baranyazici/Omni-Wheel-Robot-Development-for-Industrial-Transportation/PCB/PCB_Photos/PCB_Photo_1.jpeg

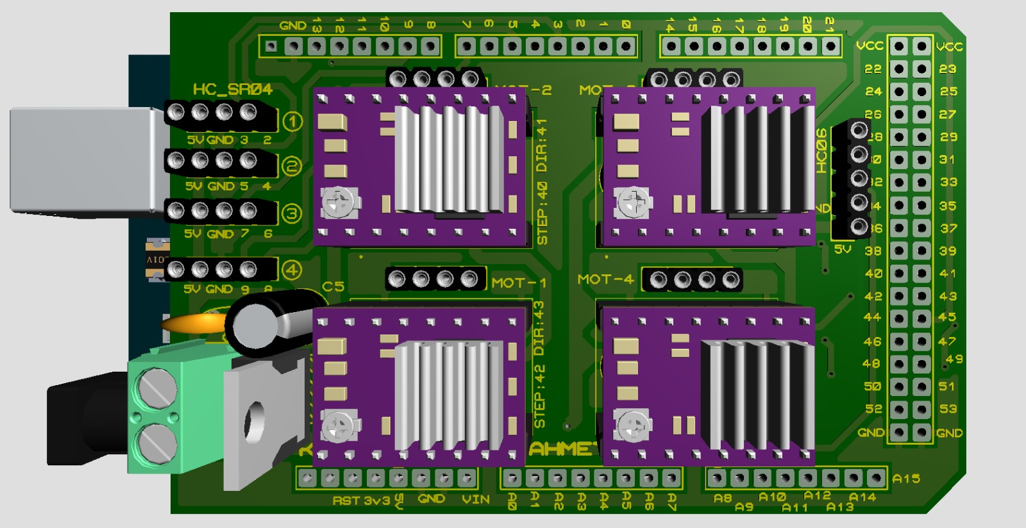
PCB/PCB_Photos/PCB_Photo_1.jpeg
