baranyazici/Omni-Wheel-Robot-Development-for-Industrial-Transportation/PCB/PCB_Photos/PCB_Photo_2.jpeg

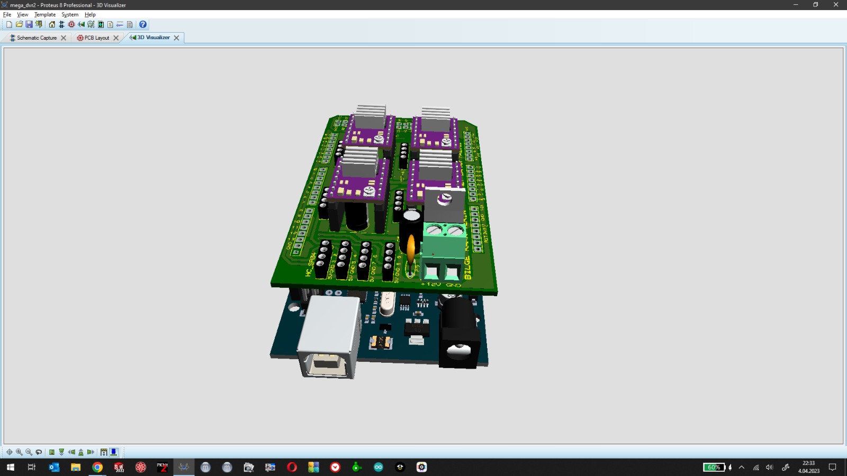
PCB/PCB_Photos/PCB_Photo_2.jpeg
