baranyazici/Omni-Wheel-Robot-Development-for-Industrial-Transportation/PCB/PCB_Photos/PCB_Photo_9.jpeg

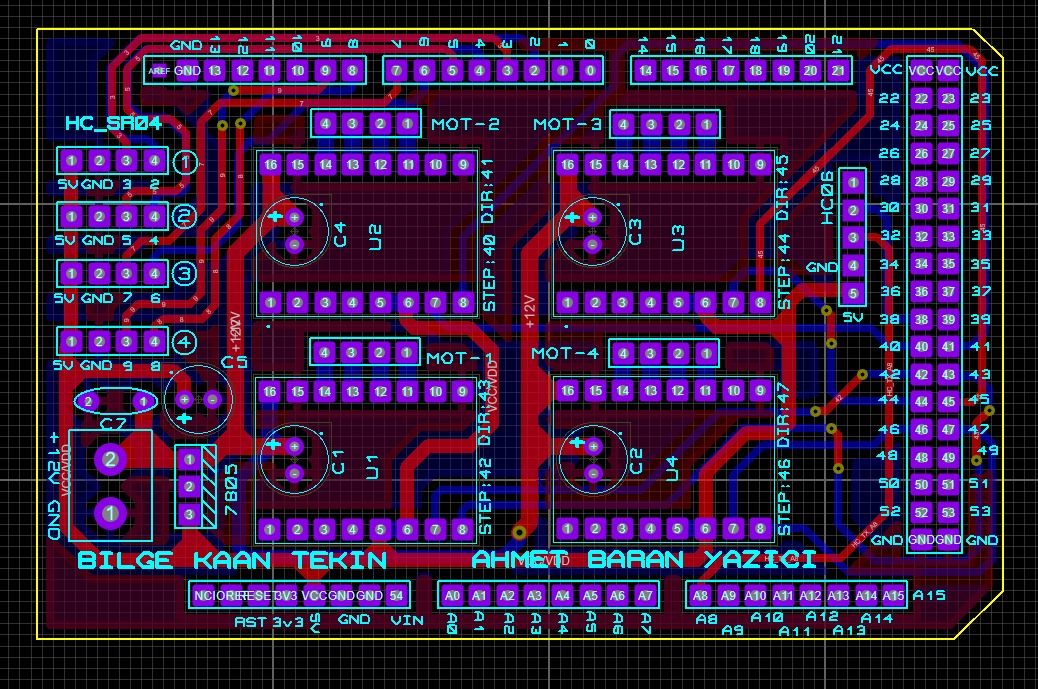
PCB/PCB_Photos/PCB_Photo_9.jpeg
