baranyazici/Omni-Wheel-Robot-Development-for-Industrial-Transportation/PCB/PCB_Photos/PCB_Photo_10.jpeg

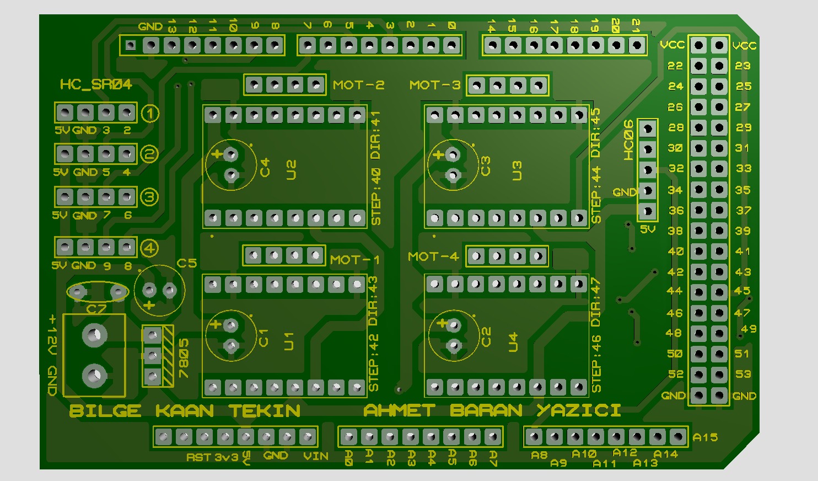
PCB/PCB_Photos/PCB_Photo_10.jpeg
