baranyazici/Omni-Wheel-Robot-Development-for-Industrial-Transportation/Photos/app_gui.jpg

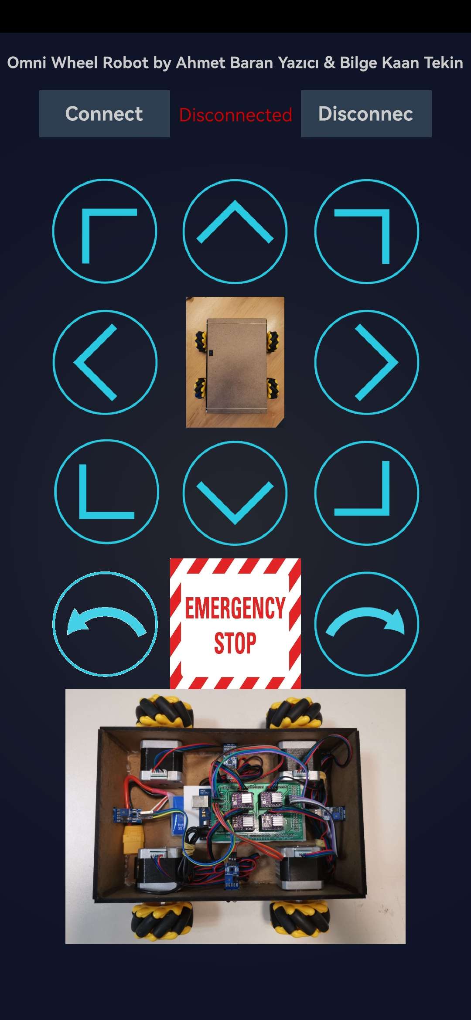
Photos/app_gui.jpg
