baranyazici/Omni-Wheel-Robot-Development-for-Industrial-Transportation/Photos/distance_sensor.jpeg

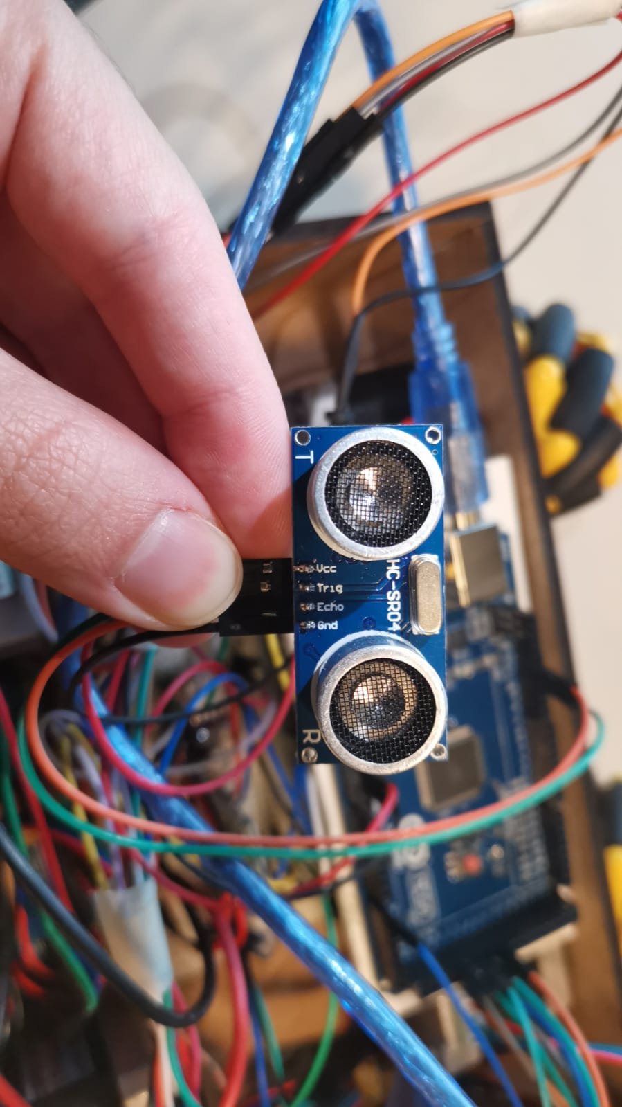
Photos/distance_sensor.jpeg
