baranyazici/Omni-Wheel-Robot-Development-for-Industrial-Transportation/Photos/distance_sensor_with_devileye.jpeg

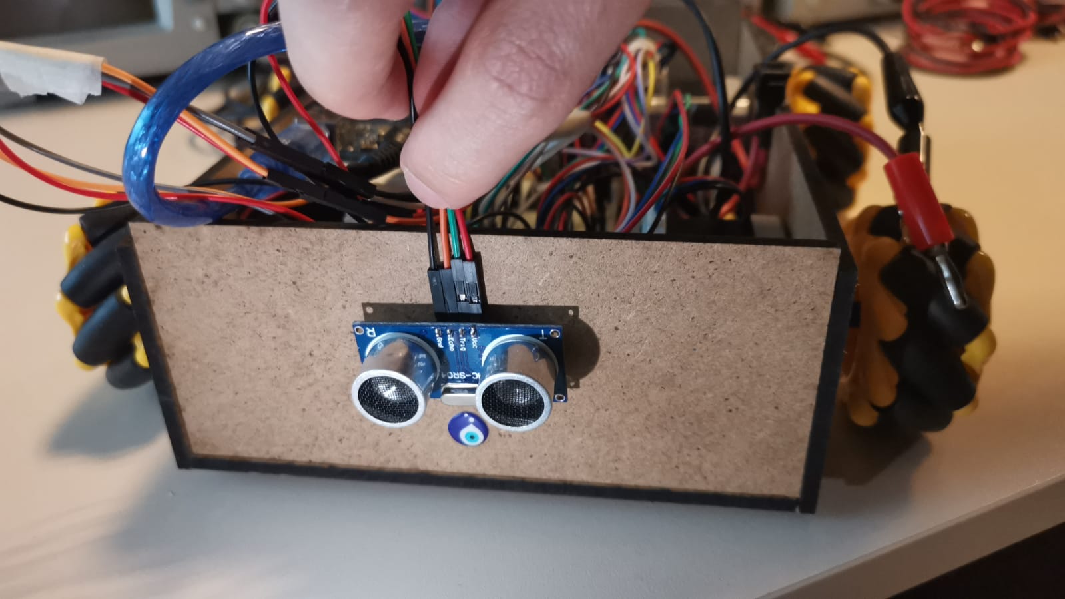
Photos/distance_sensor_with_devileye.jpeg
