baranyazici/Omni-Wheel-Robot-Development-for-Industrial-Transportation/Photos/EE401_Prototip.jpeg

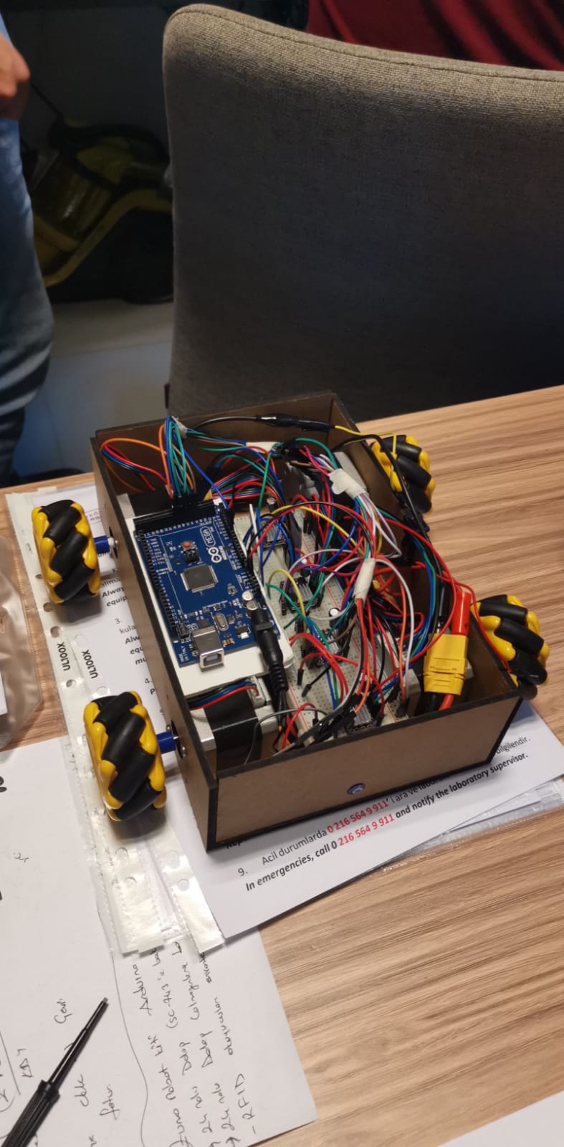
Photos/EE401_Prototip.jpeg
