baranyazici/Omni-Wheel-Robot-Development-for-Industrial-Transportation/Photos/robot_foto_2.jpeg

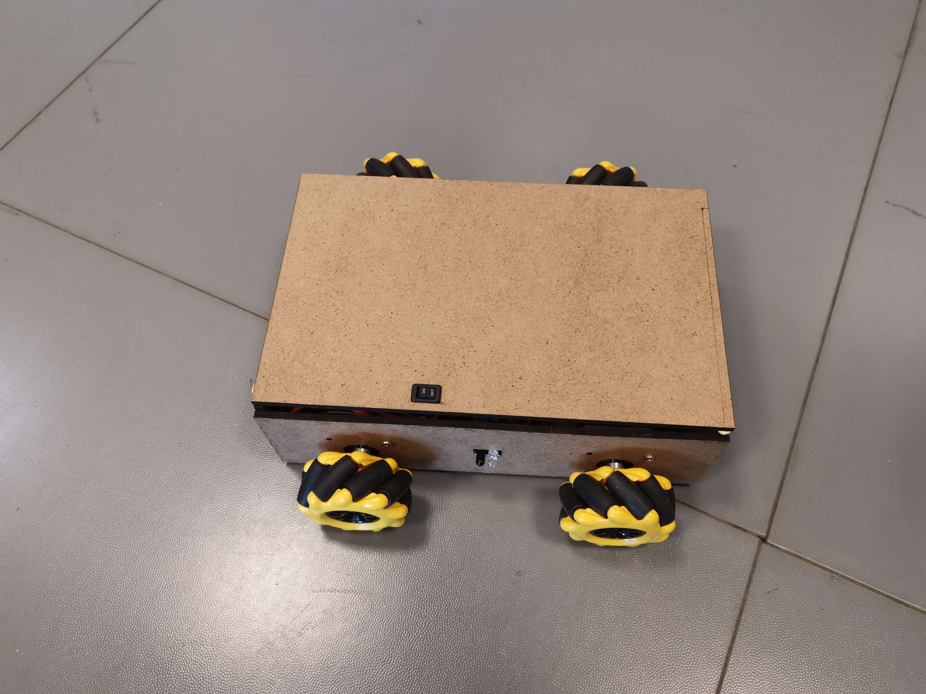
Photos/robot_foto_2.jpeg
