baranyazici/Omni-Wheel-Robot-Development-for-Industrial-Transportation/Photos/robot_foto_4.jpeg

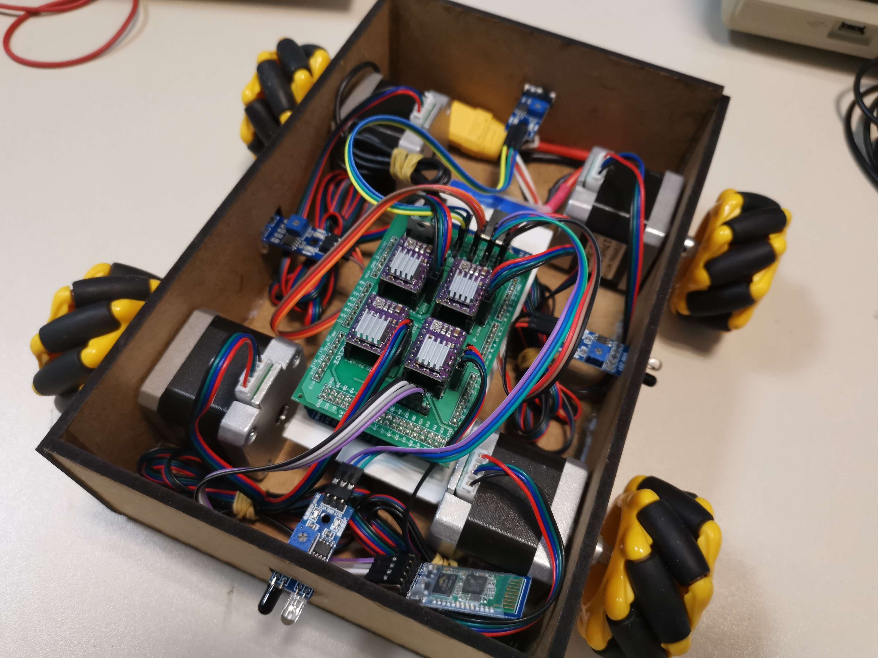
Photos/robot_foto_4.jpeg
