baranyazici/Omni-Wheel-Robot-Development-for-Industrial-Transportation/Photos/robot_foto_5.jpeg

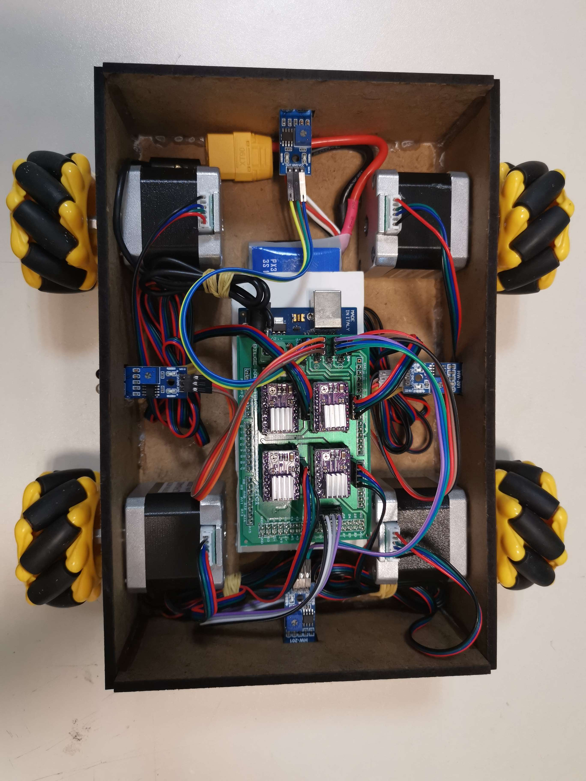
Photos/robot_foto_5.jpeg
