baranyazici/Omni-Wheel-Robot-Development-for-Industrial-Transportation/Photos/system_layout.png

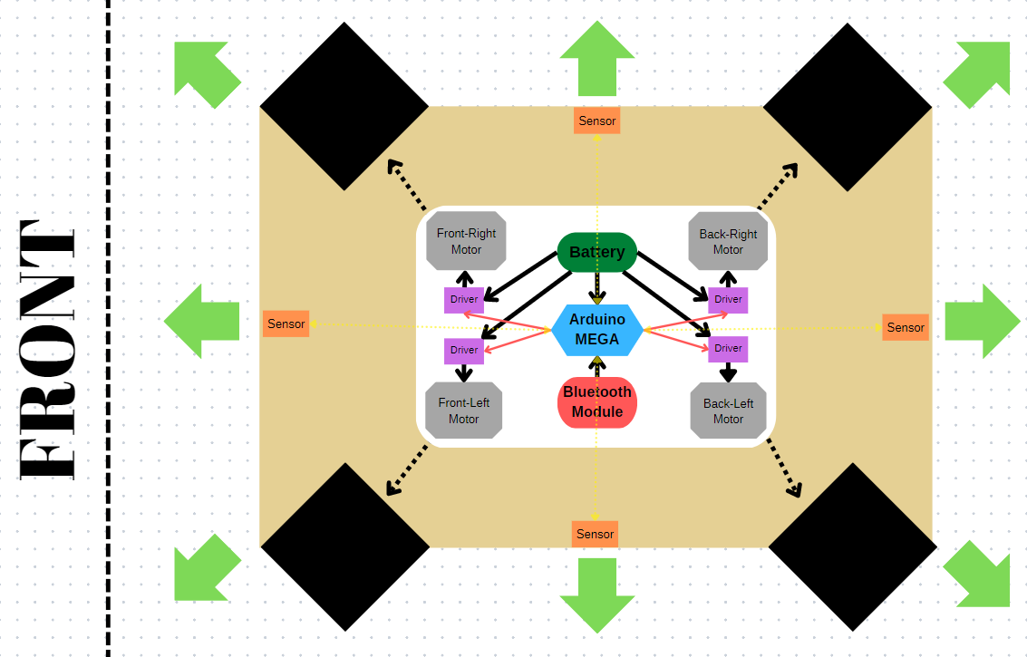
Photos/system_layout.png
