baranyazici/Omni-Wheel-Robot-Development-for-Industrial-Transportation/Photos/WhatsApp Image 2023-04-03 at 12.35.11.jpeg

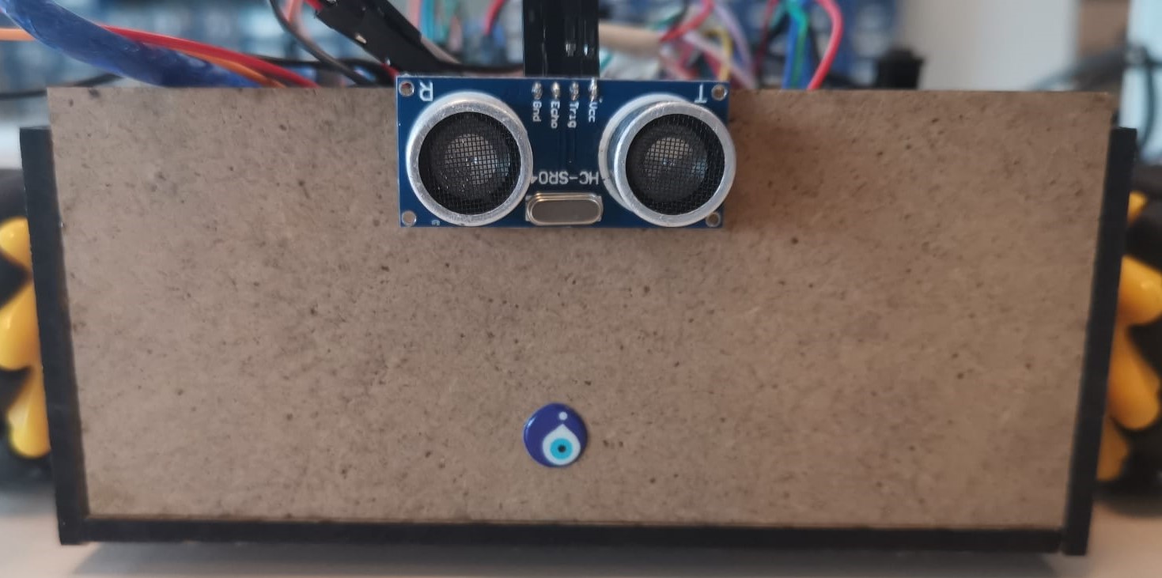
Photos/WhatsApp Image 2023-04-03 at 12.35.11.jpeg
