baranyazici/Omni-Wheel-Robot-Development-for-Industrial-Transportation/Codes/Usefull Codes/sketch_jun03b/sketch_jun03b.ino

#define ECHO 2        // Pin received echo pulse
#define TRIGGER 3     // Pin sends shot pulse

int distance; // the distance in cms         
unsigned long previousMicros = 0; // will sotre last time TRIGGER was updated    
long OnTime = 10; //microseconds of on-time     
long OffTime = 2; //microseconds of off-time    
unsigned long previousMillis = 0; //will store last time viewTime was updated   
int triggerState = LOW; // triggerState used to set it up   
long duration;   
void setup()    
{   
  Serial.begin(9600);   
  pinMode(ECHO, INPUT);   
  pinMode(TRIGGER, OUTPUT);     
}    

void loop()   
{   
  // check to see if it's time to change the state of the TRIGGER    
  unsigned long currentMicros = micros();     
  if((triggerState == LOW) && (currentMicros - previousMicros >= OffTime))     
   {      
     triggerState = HIGH; // turn it on      
     previousMicros = currentMicros; // remember the time     
     digitalWrite(TRIGGER, triggerState); // update the actual trigger     
   }    
   else if((triggerState == HIGH) && (currentMicros - previousMicros >= OnTime))    
   {           
     triggerState = LOW; // turn it off          
     previousMicros = currentMicros; // remember the time           
     digitalWrite(TRIGGER, triggerState); // update the actual trigger      
   }    



duration = pulseIn(ECHO,HIGH  );      
Serial.println(distance);        
distance = ((duration*0.034)/2);       
Serial.print("distance: ");        

}
